Ruttmann/FurbMonitoramentoIR/examples/EnviaSinalIR.ino

#include <IRremote.h>

//SPRINGER AC ON SIGNAL
const unsigned int AC_irSignal1[] PROGMEM = {9032, 4476, 580, 572, 556, 600, 556, 576, 576, 1648, 560, 1648, 580, 572, 556, 600, 556, 596, 556, 576, 576, 576, 556, 600, 552, 1648,
  556, 600, 556, 600, 556, 572, 552, 600, 556, 600, 556, 596, 556, 1648, 556, 600, 556, 572, 580, 576, 556, 596, 556, 576, 580, 572, 576, 576, 560, 596, 556, 572, 580, 1648, 560,
  572, 580, 1648, 556, 1672, 560, 572, 580, 572, 556, 600, 556, 596, 556, 576, 552, 600, 556, 576, 576, 576, 580, 572, 556, 1652, 580, 572, 552, 604, 552, 1652, 580, 1648, 556, 596,
  556, 576, 576, 10100, 8980, 4504, 556, 1672, 560, 572, 580, 576, 552, 600, 556, 576, 576, 576, 552, 1652, 580, 576, 576, 1648, 560, 1648, 580, 1648, 556, 596, 560, 572, 580, 1648,
  556, 600, 556, 576, 576, 576, 552, 600, 556, 576, 576, 1648, 556, 600, 556, 576, 576, 576, 556, 600, 552, 600, 556, 572, 556, 600, 556, 596, 556, 576, 552, 600, 556, 596, 556, 576,
  580, 572, 556, 600, 556, 576, 576, 1648, 556, 1648, 584, 572, 552, 604, 552, 600, 556, 576, 576, 576, 552, 600, 556, 576, 580, 572, 552, 604, 552, 580, 576, 572, 556};

//GREE AC ON SIGNAL
//const unsigned int AC_irSignal1[] PROGMEM = {8984, 4492, 616, 576, 616, 580, 608, 584, 608, 604, 588, 604, 588, 604, 612, 580, 584, 604, 588, 1692, 612, 604, 612, 580, 612, 1692, 612,
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
    if (i & 1)
      irsend.space(pgm_read_word_near(&signalArray[i]));
    else
      irsend.mark(pgm_read_word_near(&signalArray[i]));  
  }
  irsend.space(1);
}

void setup() {
  // put your setup code here, to run once:
  Serial.begin(115200); 
  pinMode(PIN_BUTTON, INPUT);
}

void loop() {
  unsigned int botao1 = digitalRead(PIN_BUTTON);
  if (botao1) {
      Serial.print("Starting IR transmission: ");
      Serial.println(micros());
      sendRAW_Flash(AC_irSignal1, sizeof(AC_irSignal1), 38);
      Serial.print("End of IR transmission: ");
      Serial.println(micros());
      delay(500);
  }
}
